Ryan6338/Filament-Humidity-Controller/Simulations/Boost Converter Output Filter.asc

C1: cap; 470n
C2: cap; 4.7µF
CP1: cap; 1.5p
ESR1: res; 325m
L1: ind; 10µH
LP2: ind; 500p
LP3: ind; 1.5n
R1: res; 2R
V1: voltage; ""; AC 1
Named nets: 0, 12V
LP3 includes estimated parasitic inductance
of damping resistors forming R1.
.ac oct 10 1K 1G
