Ryan6338/Filament-Humidity-Controller/Simulations/Boost Converter Transient.asc

C1: cap; 4.7µF
C2: cap; 470n
C3: cap; 470n
C4: cap; 4.7µF
CP1: cap; 1.5p
CP2: cap; 1.5p
D1: schottky; SS24
ESR1: res; 325m
ESR2: res; 325m
L1: ind; 10µH
L2: ind; 10µH
LP1: ind; 1.5n
LP2: ind; 500p
LP3: ind; 500p
LP4: ind; 1.5n
M1: nmos; BSH114
R1: res; 2R
R2: res; 2R
R_LOAD: res; 60R
V1: voltage; 5V
V2: voltage; PULSE(0 5 0 30n 30n {Ton} {Period} 1G)
Named nets: 0, 12V, BST_12V
NOTES:
1. BSH114 has similar on-resistance to the internal FET in the LM27313 IC.
2. Rise time of V2 has been tuned to achieve a 10ns rise time of M1.
.tran 2m
.param Fsw=1.6Meg
.param DC=0.6079
 
.param Period=1/Fsw
.param Ton=Period*DC
